OSLUV/OpenLuminaire-Hardware/v4/electrical/cables/xarp-04v_xa_housing.step

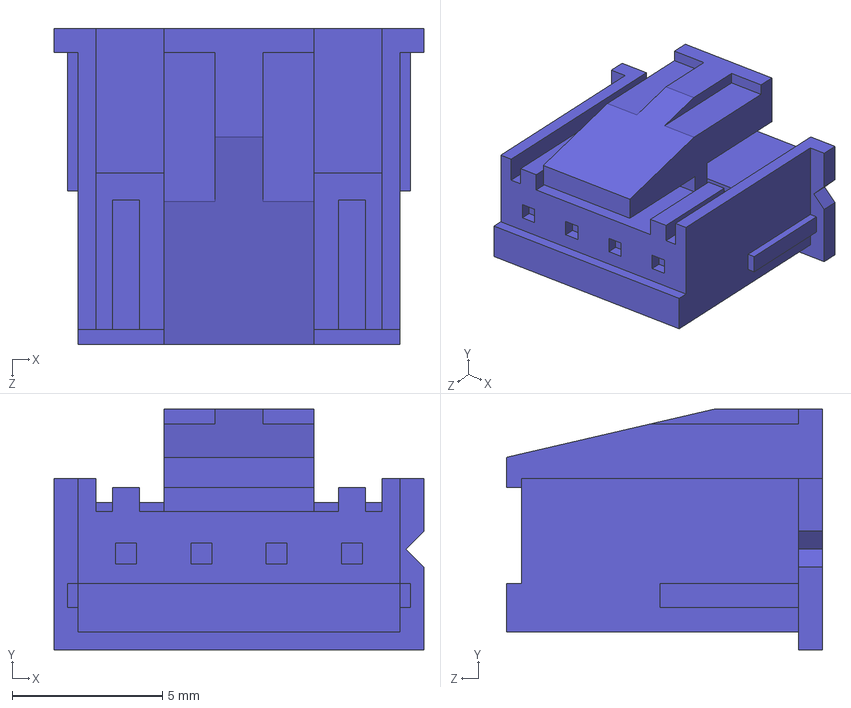
[picture p16: CAD file, 2025-05-12]
v4/electrical/cables/xarp-04v_xa_housing.step
12.3 x 8.00 x 10.5 mm
