OSLUV/OpenLuminaire-Hardware/v4/electrical/models/fh35-15s-0.3shw(50)_connector.step

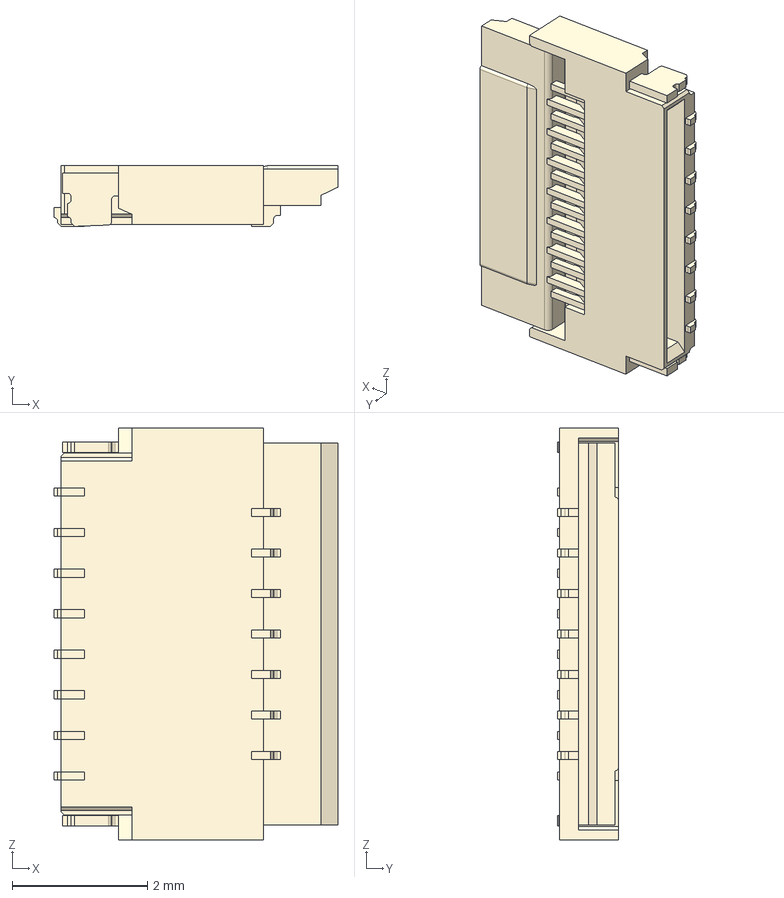
[picture p17: CAD file, 2025-05-12]
v4/electrical/models/fh35-15s-0.3shw(50)_connector.step
4.20 x 0.9 x 6.10 mm
