OSLUV/OpenLuminaire-Hardware/v4/mechanical/printable_files/emitter_pxz120i3_ballast_spacer.step

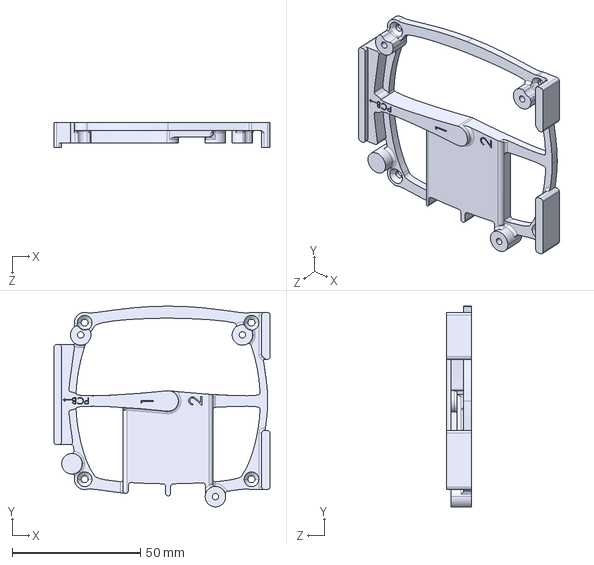
[picture p18: CAD file, 2025-05-12]
v4/mechanical/printable_files/emitter_pxz120i3_ballast_spacer.step
84.1 x 78.2 x 9.60 mm
