OSLUV/OpenLuminaire-Hardware/v4/electrical/models/xl-1608uwc-04_led.step

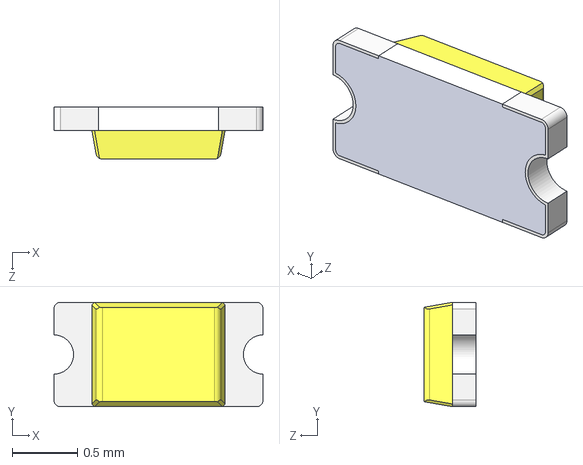
[picture p19: CAD file, 2025-05-12]
v4/electrical/models/xl-1608uwc-04_led.step
1.60 x 0.8 x 0.4 mm
