OSLUV/OpenLuminaire-Hardware/v4/mechanical/b5p-vh_jst_vh_connector.sldprt

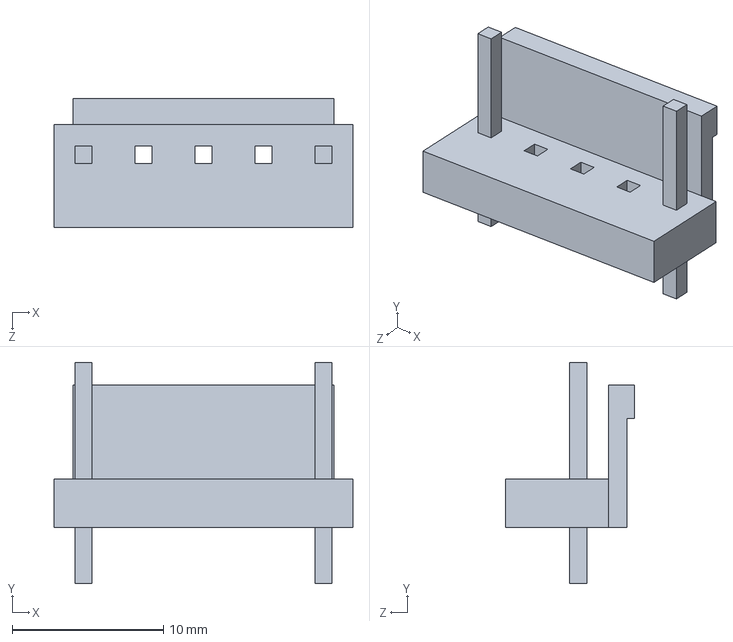
[picture p20: CAD file, 2025-05-12]
v4/mechanical/b5p-vh_jst_vh_connector.sldprt
19.7 x 14.6 x 8.50 mm
