OSLUV/OpenLuminaire-Hardware/v4/mechanical/printable_files/shim.step

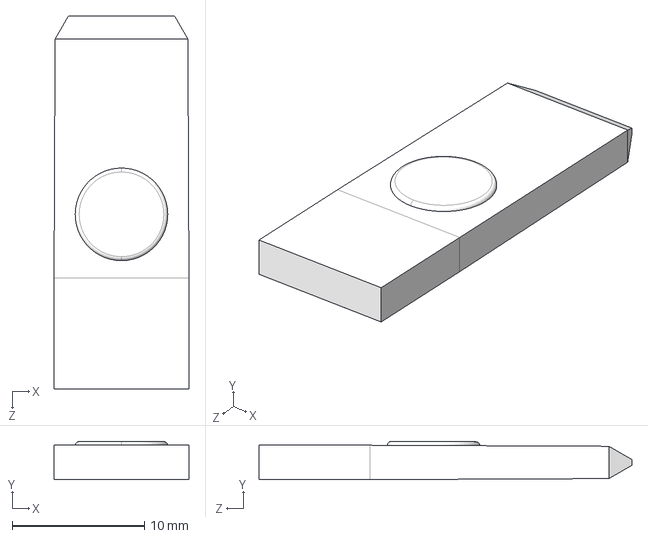
[picture p21: CAD file, 2025-05-12]
v4/mechanical/printable_files/shim.step
10.2 x 2.89 x 28.2 mm
