OSLUV/OpenLuminaire-Hardware/v4/electrical/models/stusb4500.step

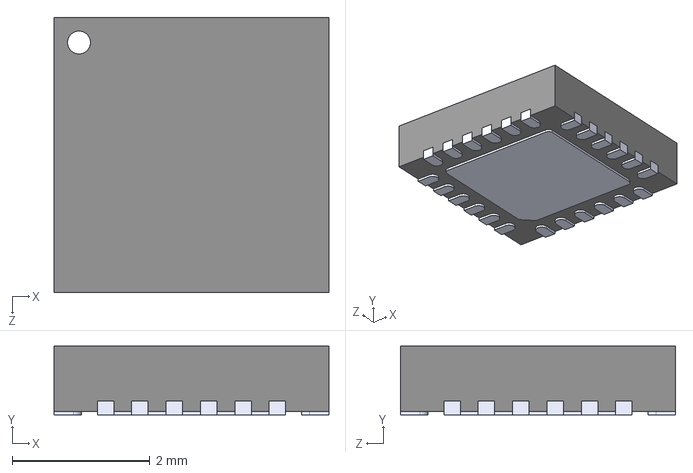
[picture p22: CAD file, 2025-05-12]
v4/electrical/models/stusb4500.step
4.00 x 1.00 x 4.00 mm
