OSLUV/OpenLuminaire-Hardware/v4/mechanical/printable_files/lens_cap.step

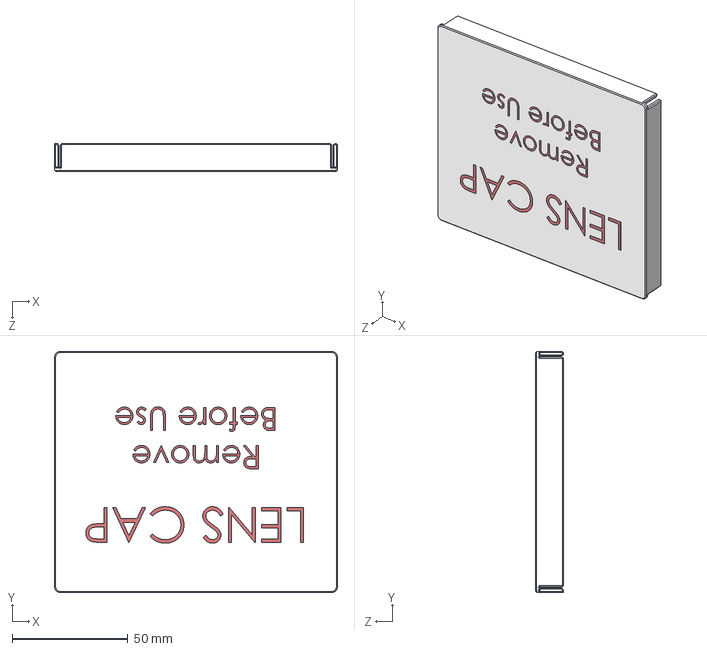
[picture p23: CAD file, 2025-05-12]
v4/mechanical/printable_files/lens_cap.step
122.0 x 104.0 x 12.0 mm
