OSLUV/OpenLuminaire-Hardware/v4/electrical/models/tsc015a06026a_6mm_button.sldprt

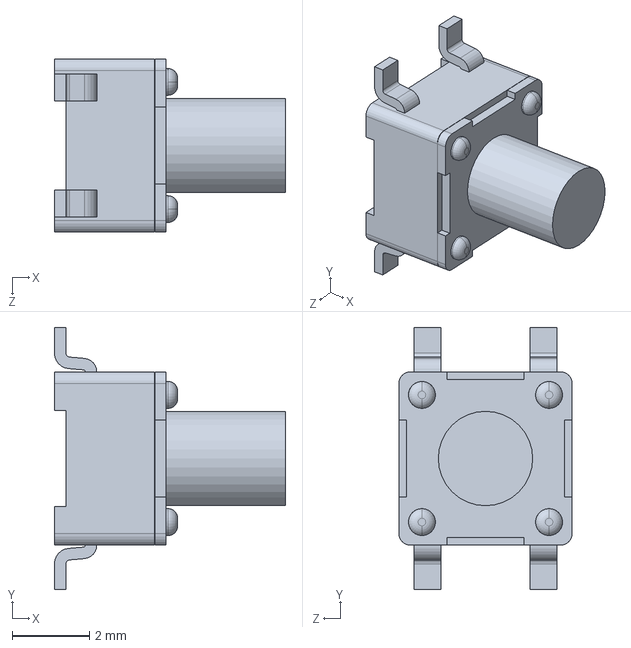
[picture p24: CAD file, 2025-05-12]
v4/electrical/models/tsc015a06026a_6mm_button.sldprt
6.00 x 6.80 x 4.50 mm
