OSLUV/OpenLuminaire-Hardware/v4/mechanical/printable_files/back_plate.step

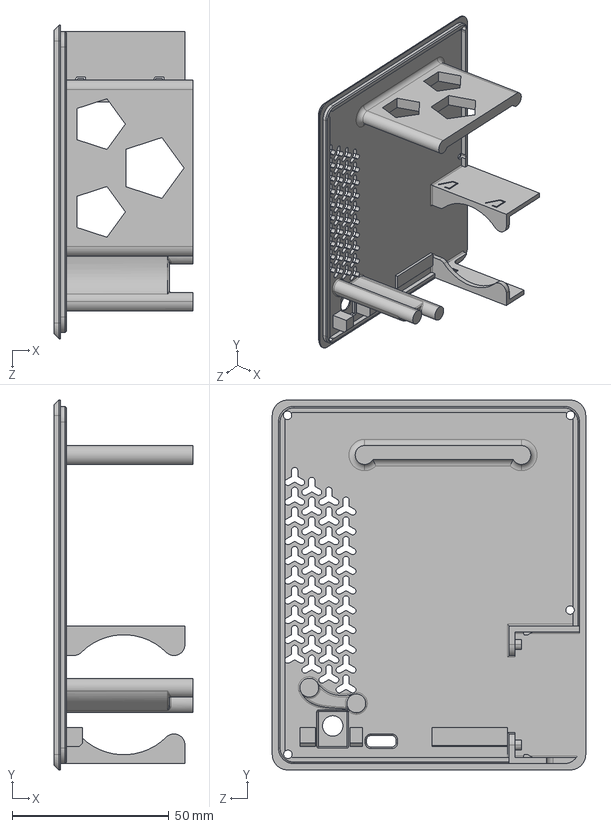
[picture p25: CAD file, 2025-05-12]
v4/mechanical/printable_files/back_plate.step
44.2 x 118.0 x 100.0 mm
