OSLUV/OpenLuminaire-Hardware/v4/electrical/cables/jumper_wire.sldprt

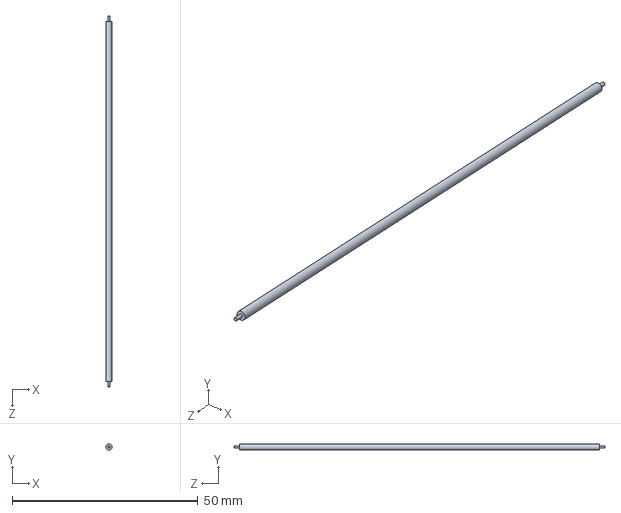
[picture p26: CAD file, 2025-05-12]
v4/electrical/cables/jumper_wire.sldprt
1.70 x 1.70 x 100.0 mm
