OSLUV/OpenLuminaire-Hardware/v4/electrical/models/5-pin_female_header.step

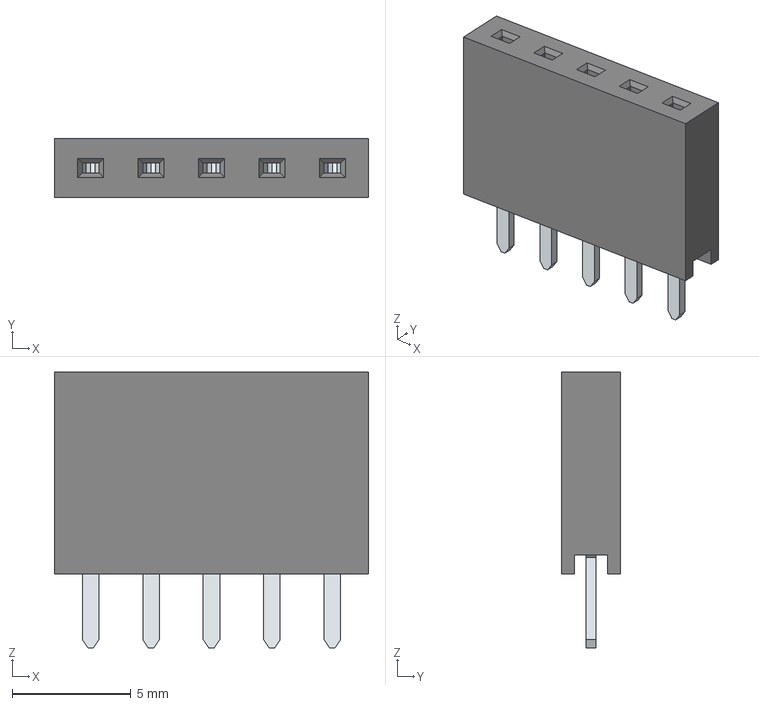
[picture p27: CAD file, 2025-05-12]
v4/electrical/models/5-pin_female_header.step
13.2 x 2.50 x 11.6 mm
