OSLUV/OpenLuminaire-Hardware/v4/electrical/cables/vhr-5n_jst_xh_housing.step

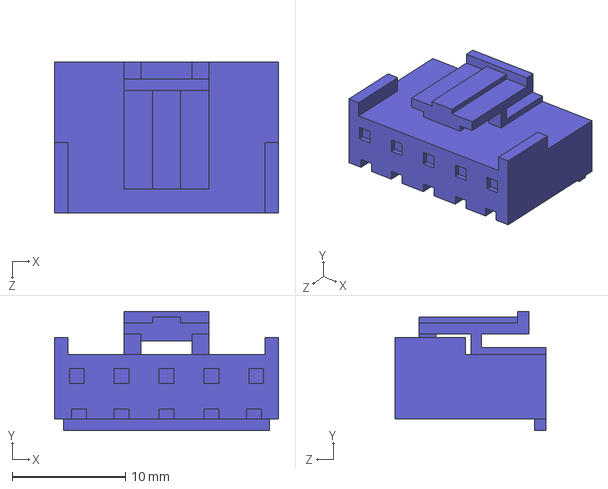
[picture p28: CAD file, 2025-05-12]
v4/electrical/cables/vhr-5n_jst_xh_housing.step
19.7 x 10.5 x 13.3 mm
