OSLUV/OpenLuminaire-Hardware/v4/electrical/models/tsc015a08026b_8mm_button.sldprt

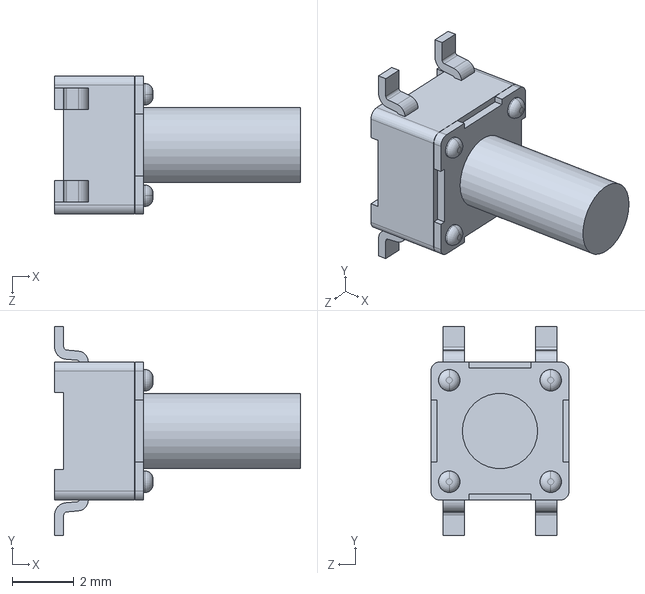
[picture p29: CAD file, 2025-05-12]
v4/electrical/models/tsc015a08026b_8mm_button.sldprt
8.00 x 6.80 x 4.50 mm
