OSLUV/OpenLuminaire-Hardware/v4/mechanical/hlk-ld2410c_radar.sldprt

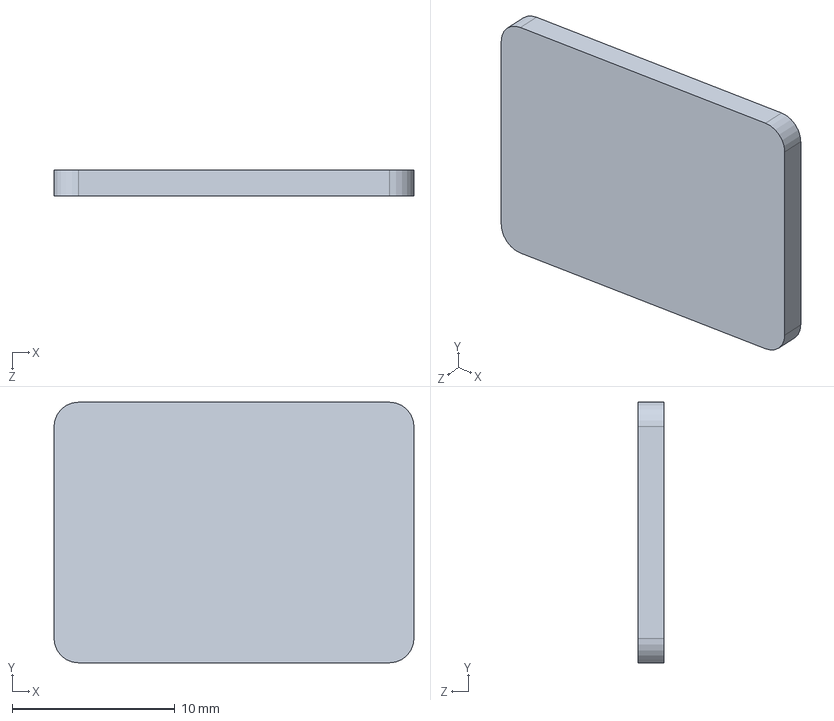
[picture p30: CAD file, 2025-05-02]
v4/mechanical/hlk-ld2410c_radar.sldprt
22.1 x 16.0 x 1.60 mm
