OSLUV/OpenLuminaire-Hardware/v4/electrical/cables/hv_wire.sldprt

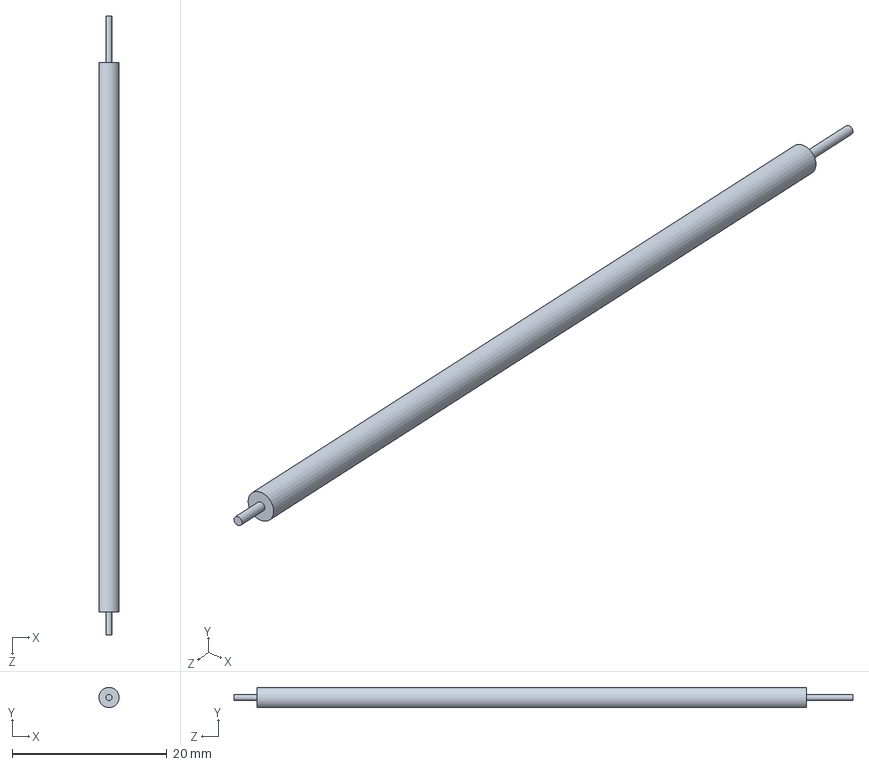
[picture p31: CAD file, 2025-05-12]
v4/electrical/cables/hv_wire.sldprt
2.62 x 2.62 x 80.0 mm
