OSLUV/OpenLuminaire-Hardware/v4/electrical/models/radar_straight.step

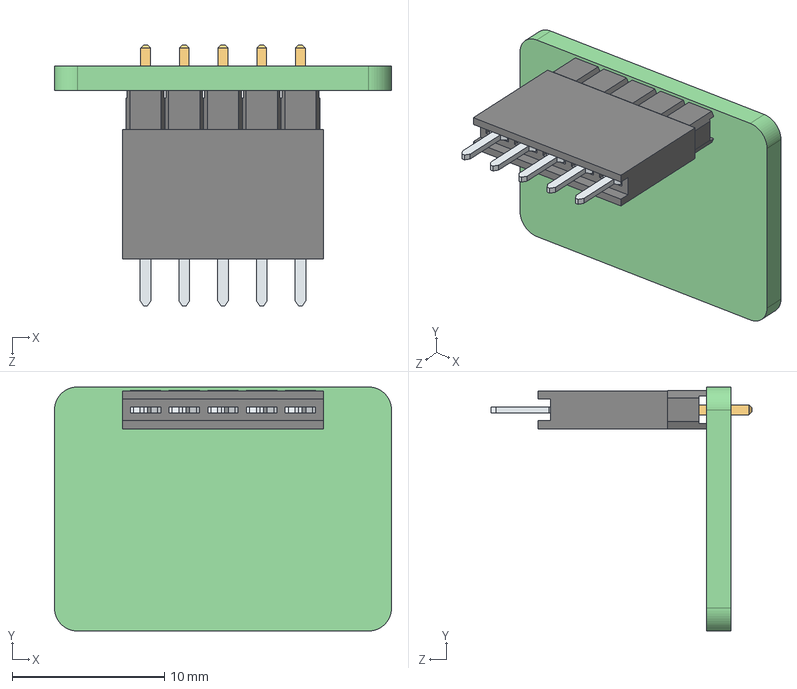
[picture p32: CAD file, 2025-05-12]
v4/electrical/models/radar_straight.step
22.1 x 16.0 x 17.1 mm
hlk-ld2410c_radar
6130xx11821_PIN.step x 5
61300511821.step
