OSLUV/OpenLuminaire-Hardware/v4/electrical/models/bm02b-srss-tb_jst_sh_connector.step

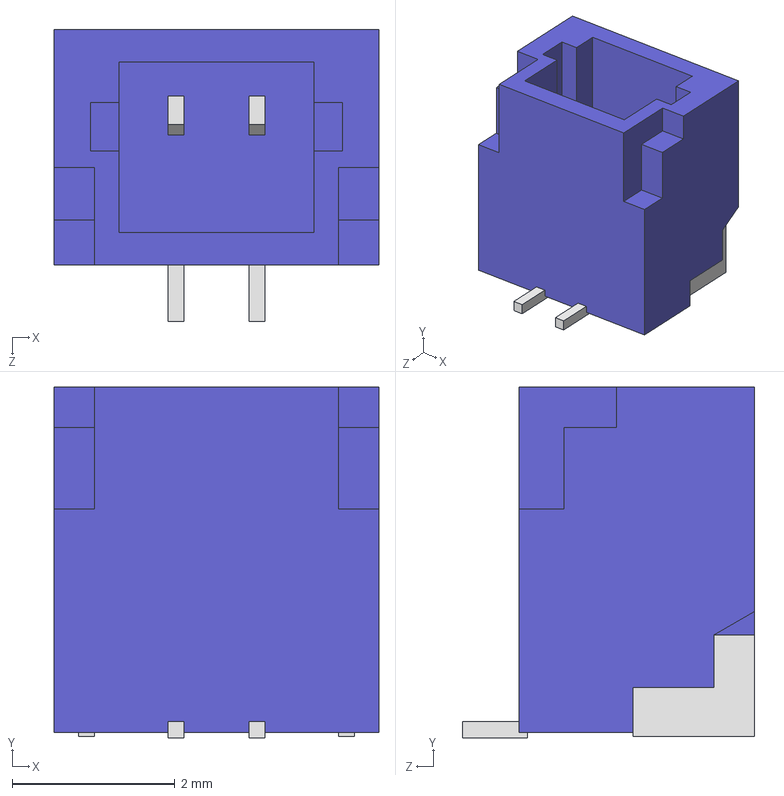
[picture p33: CAD file, 2025-05-12]
v4/electrical/models/bm02b-srss-tb_jst_sh_connector.step
4.00 x 4.32 x 3.60 mm
