OSLUV/OpenLuminaire-Hardware/v4/electrical/cables/sxa-001t-p0.6_xa_contact.step

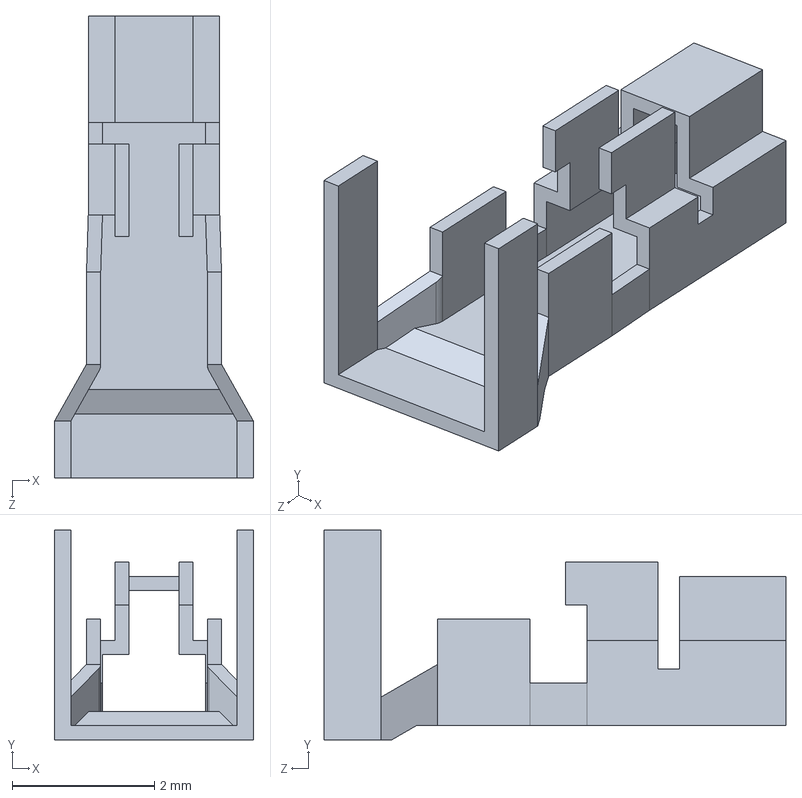
[picture p34: CAD file, 2025-05-12]
v4/electrical/cables/sxa-001t-p0.6_xa_contact.step
2.80 x 2.95 x 6.50 mm
