OSLUV/OpenLuminaire-Hardware/v4/electrical/models/sm02b-srss-tb_jst_sh_connector.step

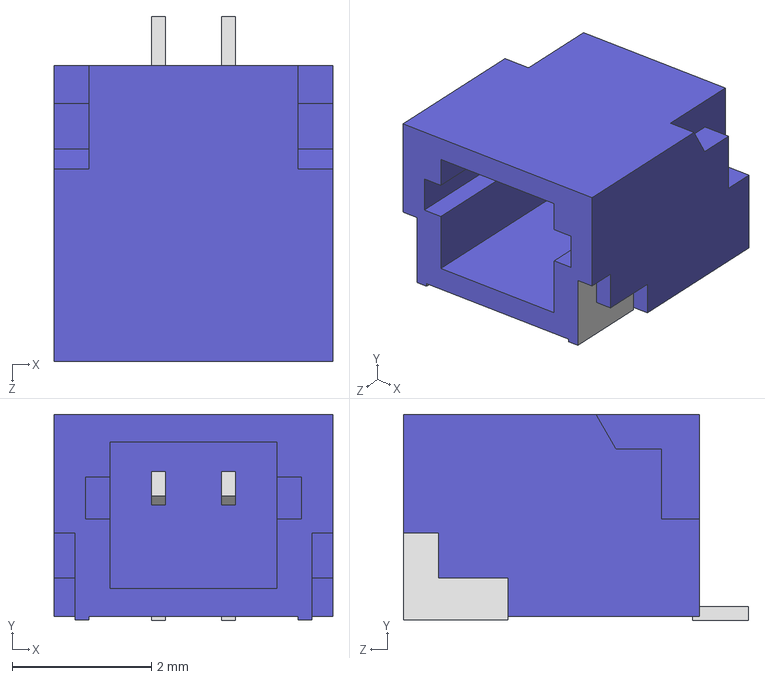
[picture p35: CAD file, 2025-05-12]
v4/electrical/models/sm02b-srss-tb_jst_sh_connector.step
4.00 x 2.96 x 4.95 mm
