OSLUV/OpenLuminaire-Hardware/v4/electrical/models/dc-005_2.0_barrel_jack.sldprt

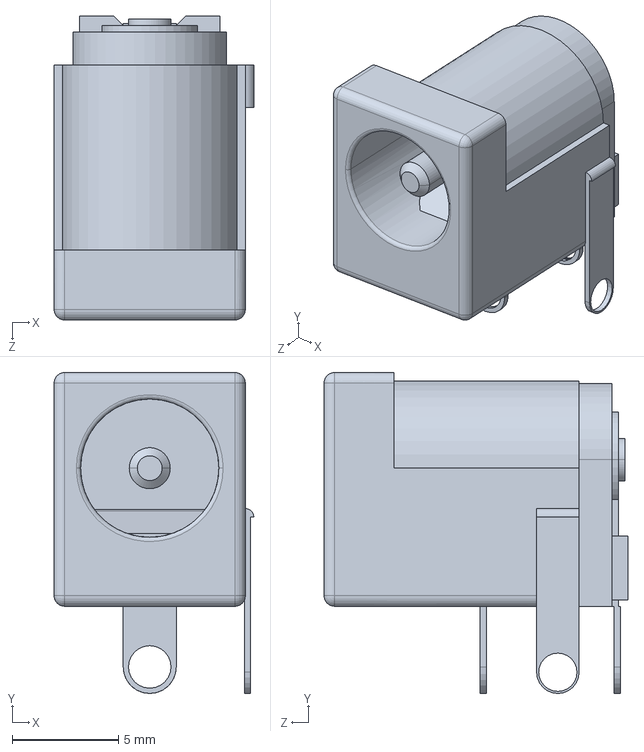
[picture p36: CAD file, 2025-05-12]
v4/electrical/models/dc-005_2.0_barrel_jack.sldprt
9.40 x 15.1 x 14.3 mm
