OSLUV/OpenLuminaire-Hardware/v4/electrical/models/b04b-xask-1_connector.step

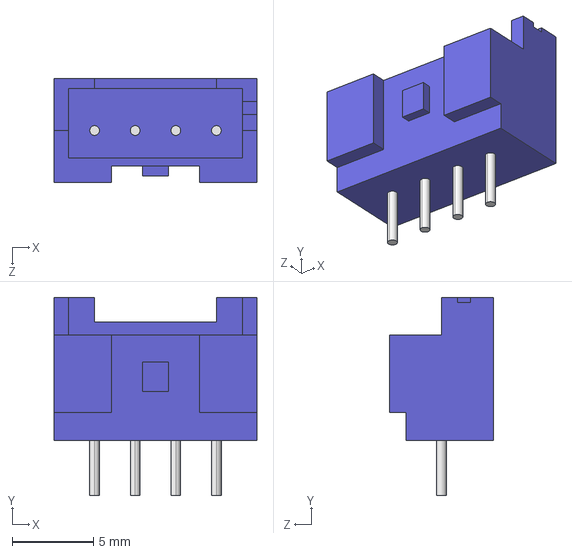
[picture p37: CAD file, 2025-05-12]
v4/electrical/models/b04b-xask-1_connector.step
12.5 x 12.2 x 6.40 mm
