OSLUV/OpenLuminaire-Hardware/v4/electrical/models/pj-002ah_connector.step

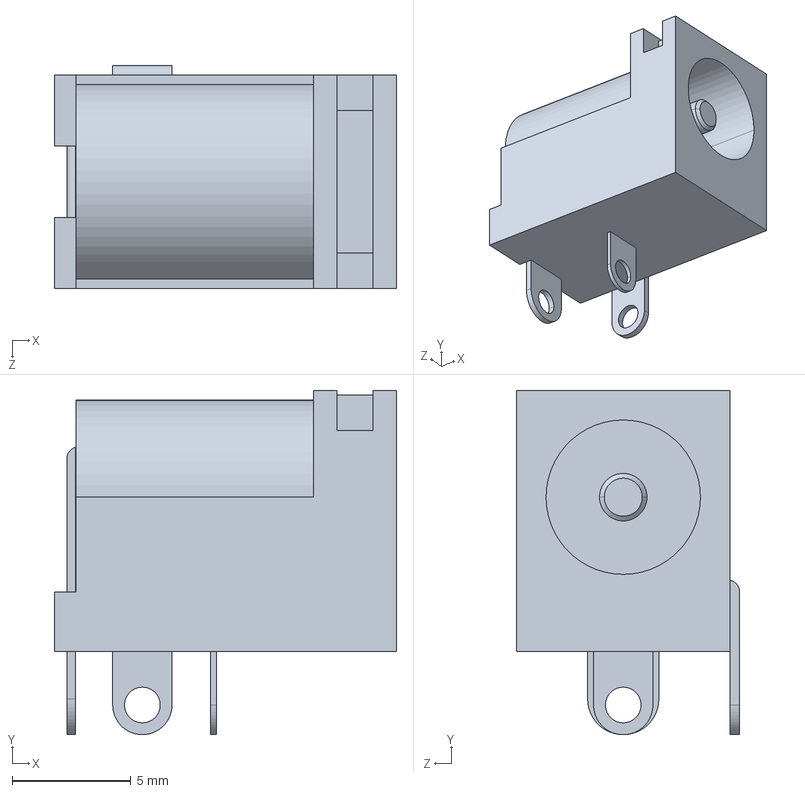
[picture p38: CAD file, 2025-05-12]
v4/electrical/models/pj-002ah_connector.step
14.4 x 14.5 x 9.40 mm
