OSLUV/OpenLuminaire-Hardware/v4/electrical/models/er-tft1.54-2_lcd.sldprt

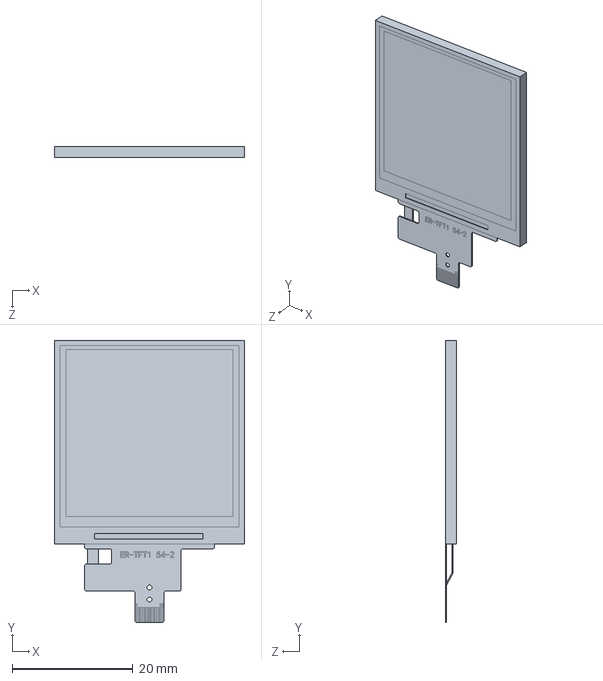
[picture p39: CAD file, 2025-05-12]
v4/electrical/models/er-tft1.54-2_lcd.sldprt
31.5 x 46.7 x 1.90 mm
