OSLUV/OpenLuminaire-Hardware/v4/electrical/models/b05b-xask-1_connector.step

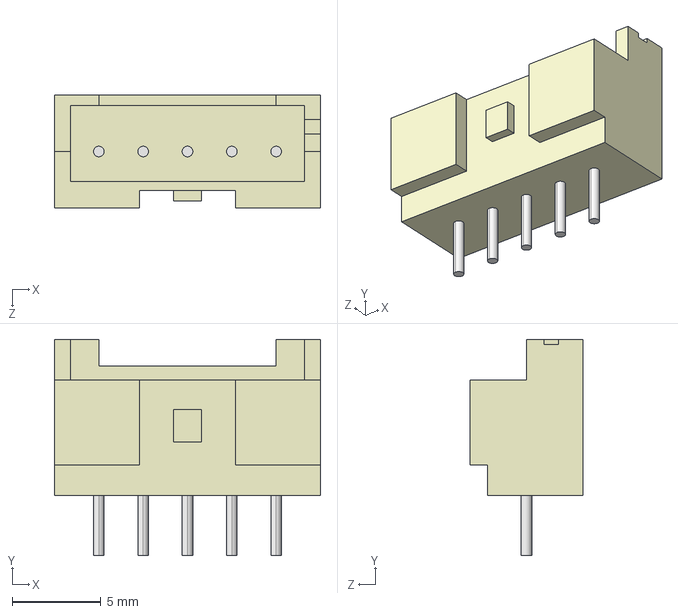
[picture p40: CAD file, 2025-05-12]
v4/electrical/models/b05b-xask-1_connector.step
15.0 x 12.2 x 6.40 mm
