OSLUV/OpenLuminaire-Hardware/v4/electrical/models/radar_angled_1.step

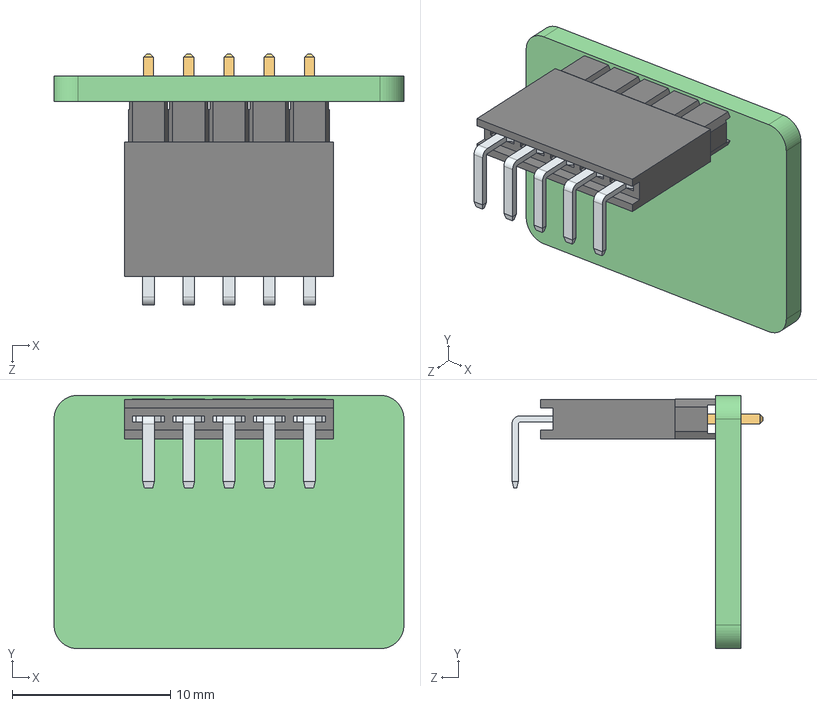
[picture p41: CAD file, 2025-05-12]
v4/electrical/models/radar_angled_1.step
22.1 x 16.0 x 15.8 mm
hlk-ld2410c_radar
61300511821.step
6130xx143121_PIN.step x 5
