OSLUV/OpenLuminaire-Hardware/v4/electrical/models/b5p-vh_jst_vh_connector.step

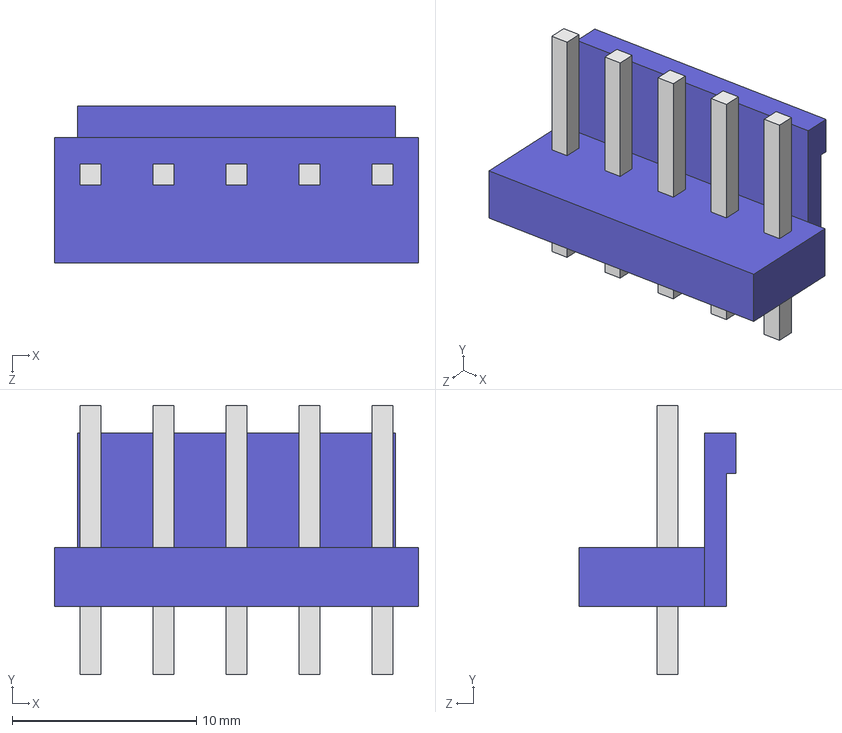
[picture p42: CAD file, 2025-05-12]
v4/electrical/models/b5p-vh_jst_vh_connector.step
19.7 x 14.6 x 8.50 mm
