OSLUV/OpenLuminaire-Hardware/v4/electrical/models/er-tft1.54-2_lcd_bend1.sldprt

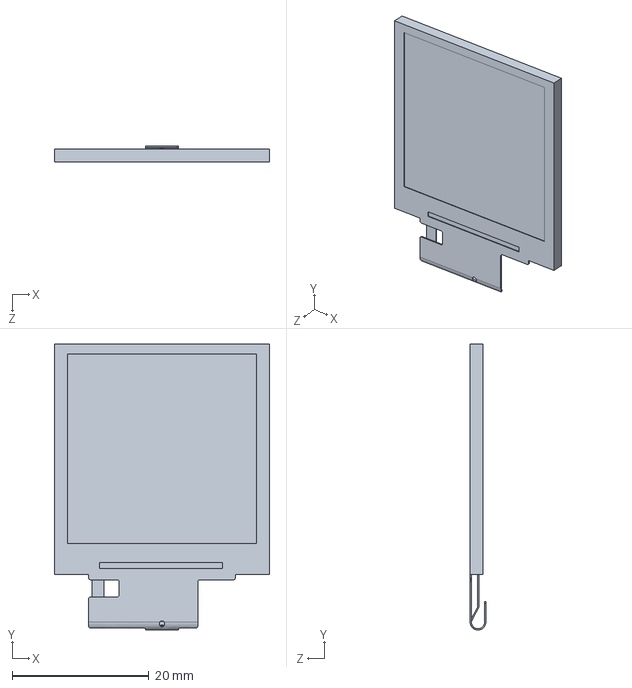
[picture p44: CAD file, 2025-05-12]
v4/electrical/models/er-tft1.54-2_lcd_bend1.sldprt
31.5 x 41.9 x 2.31 mm
