OSLUV/OpenLuminaire-Hardware/v4/electrical/models/er-tft1.54-2_lcd_bend2.sldprt

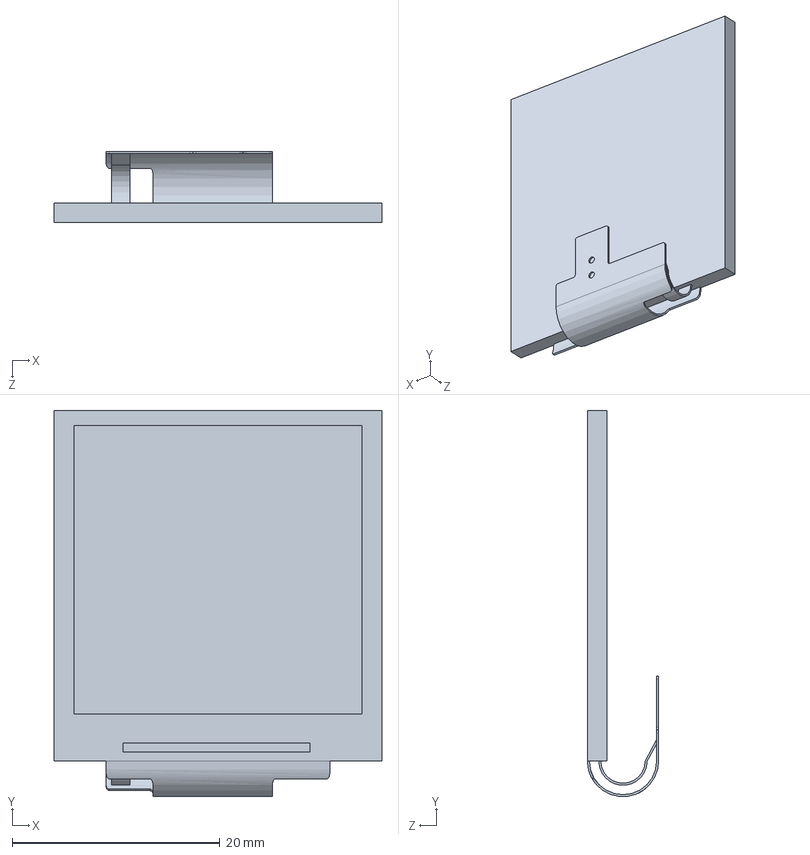
[picture p45: CAD file, 2025-05-12]
v4/electrical/models/er-tft1.54-2_lcd_bend2.sldprt
31.5 x 37.1 x 6.86 mm
