OSLUV/OpenLuminaire-Hardware/v4/electrical/models/5-pin_female_header_right_angle.step

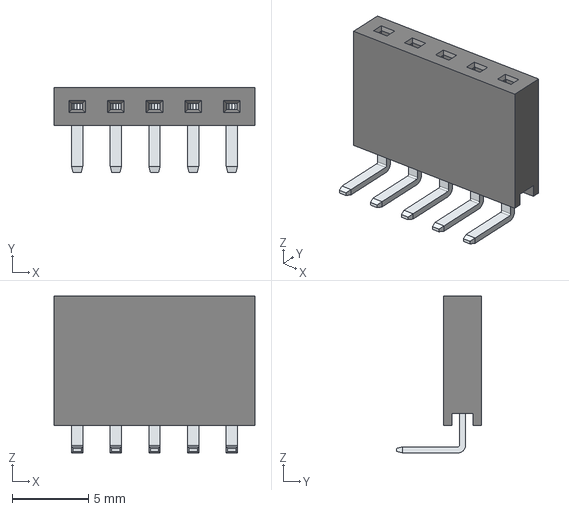
[picture p46: CAD file, 2025-05-12]
v4/electrical/models/5-pin_female_header_right_angle.step
13.2 x 5.59 x 10.3 mm
6130xx143121_PIN x 5
