OSLUV/OpenLuminaire-Hardware/v4/electrical/models/dc0053_connector.step

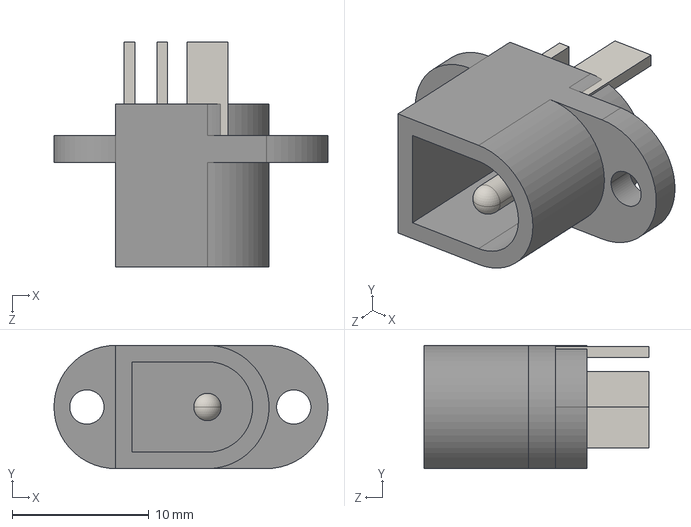
[picture p47: CAD file, 2025-05-02]
v4/electrical/models/dc0053_connector.step
20.0 x 9.00 x 16.4 mm
