OSLUV/OpenLuminaire-Hardware/v4/electrical/models/s04b-xask-1.step

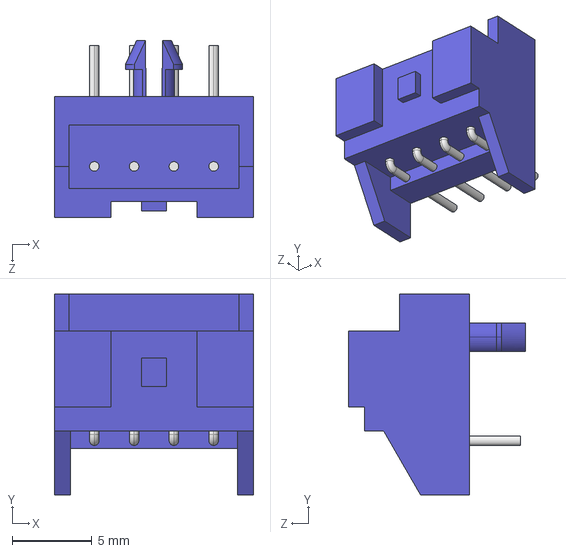
[picture p48: CAD file, 2025-05-02]
v4/electrical/models/s04b-xask-1.step
12.5 x 12.6 x 11.1 mm
